thekr1s/esp8266_wordclock/images/handleiding/Aansluiting_1.jpg

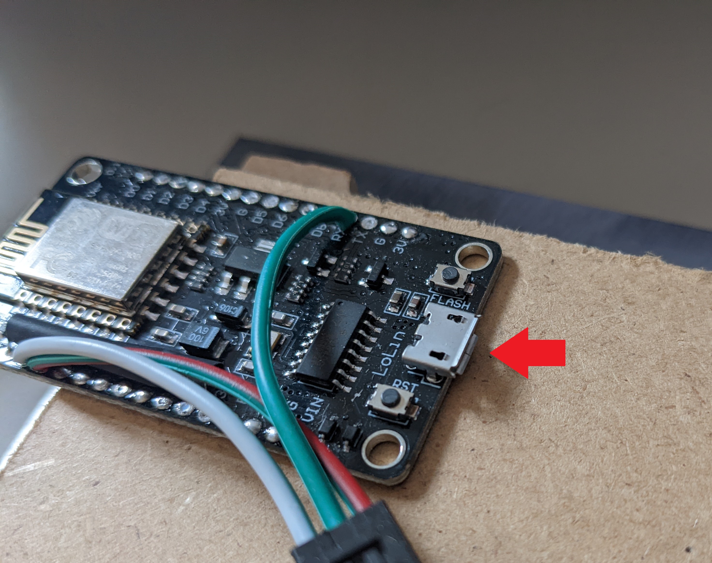
images/handleiding/Aansluiting_1.jpg
