thekr1s/esp8266_wordclock/images/rhu/2015-12-30 12.20.55.jpg

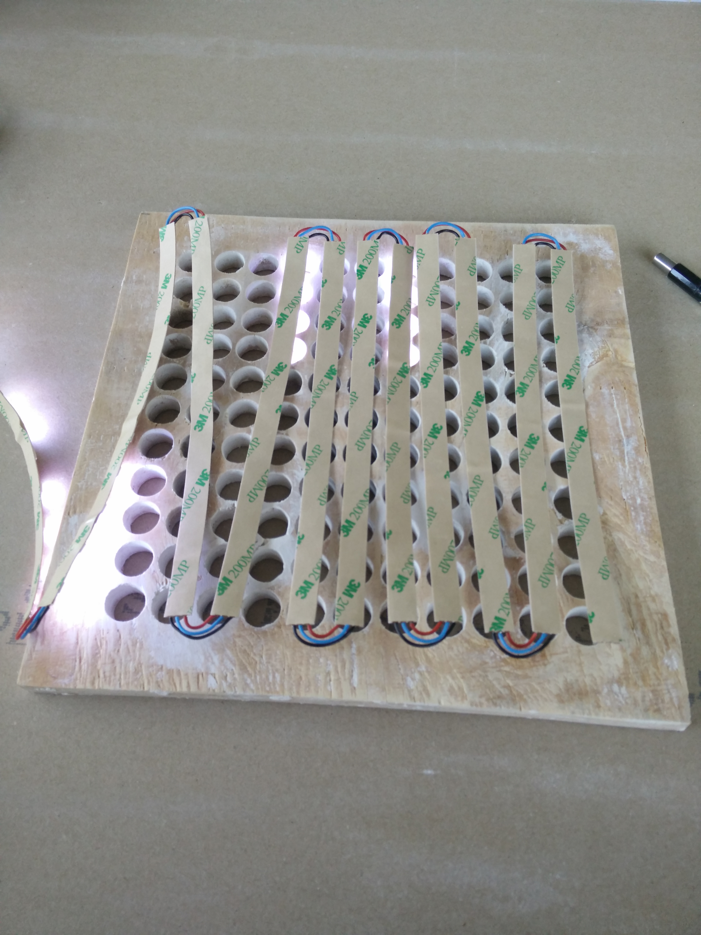
images/rhu/2015-12-30 12.20.55.jpg
