thekr1s/esp8266_wordclock/images/rhu/2016-01-02 10.30.15.jpg

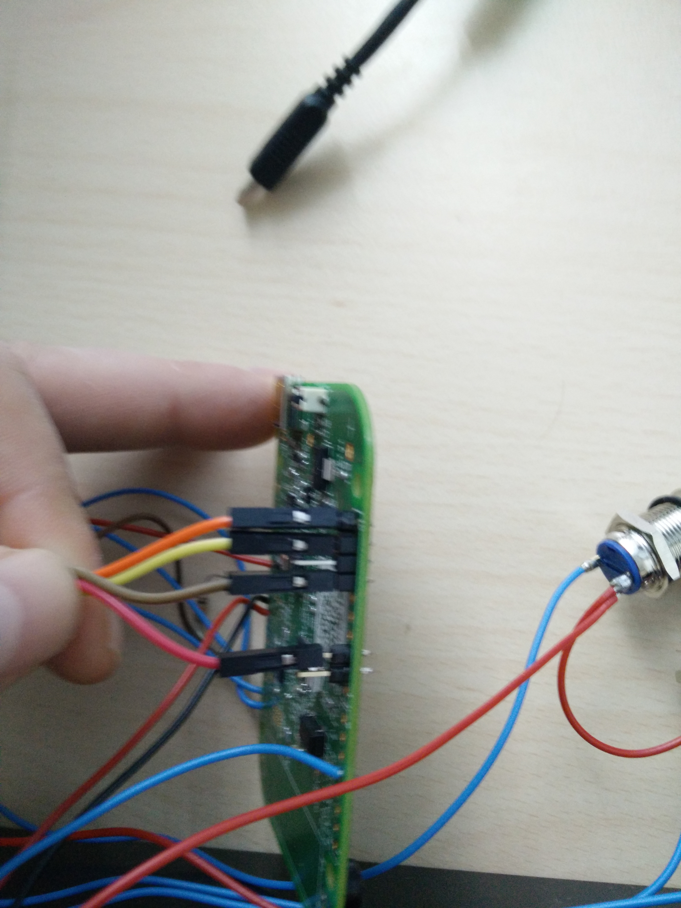
images/rhu/2016-01-02 10.30.15.jpg
