thekr1s/esp8266_wordclock/images/rwa/20151119_205304231.jpg

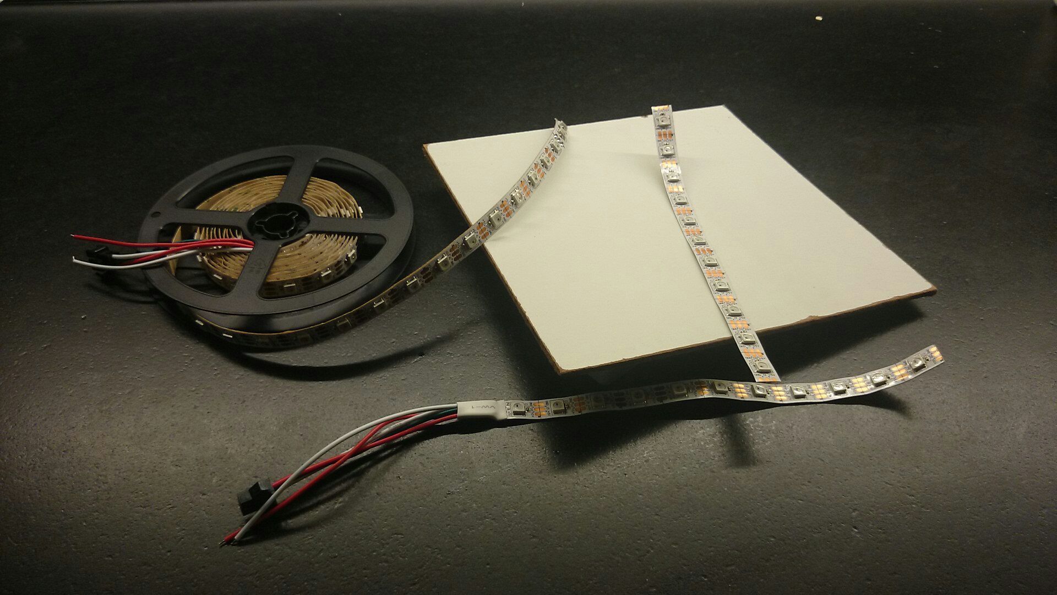
images/rwa/20151119_205304231.jpg
