thekr1s/esp8266_wordclock/images/rwa/20151119_211505547.jpg

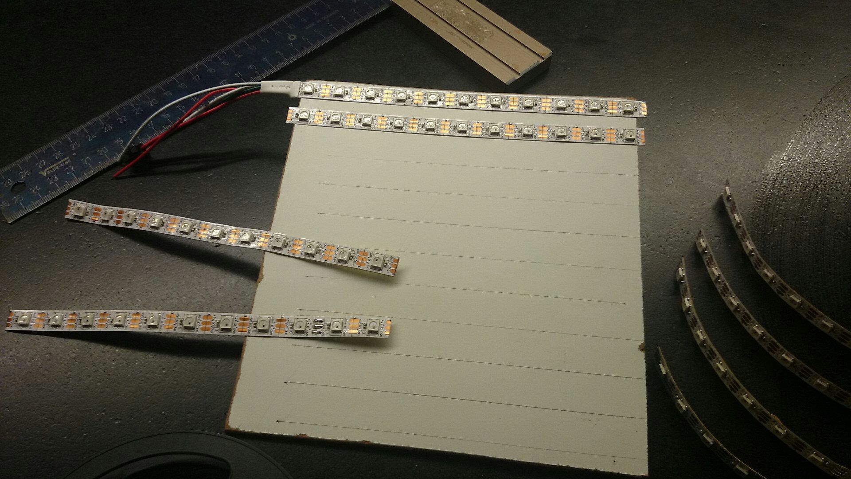
images/rwa/20151119_211505547.jpg
