thekr1s/esp8266_wordclock/images/rwa/20151119_221903994.jpg

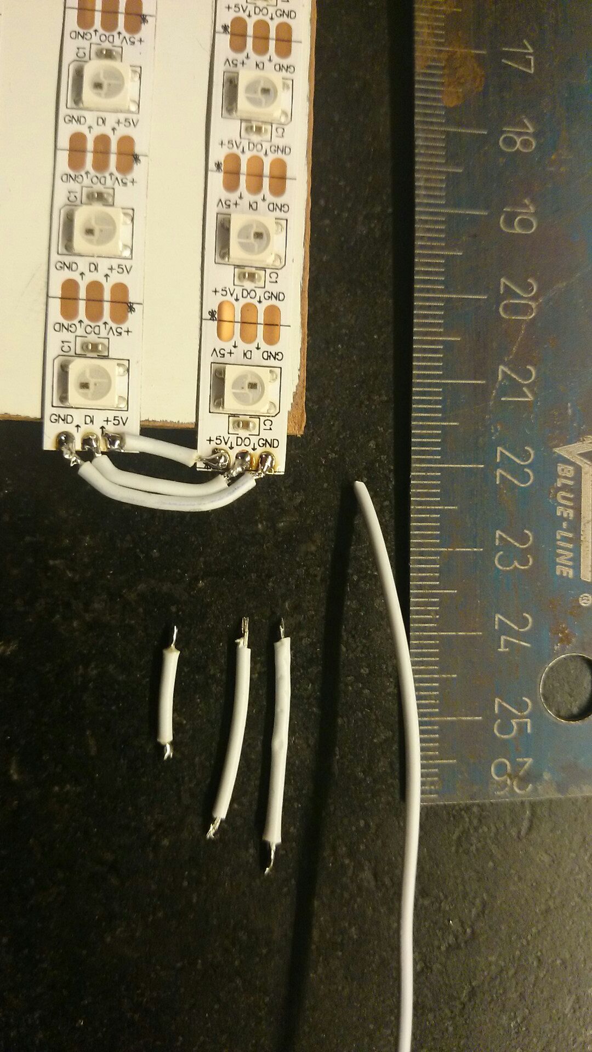
images/rwa/20151119_221903994.jpg
