thekr1s/esp8266_wordclock/images/rwa/20151119_222014442.jpg

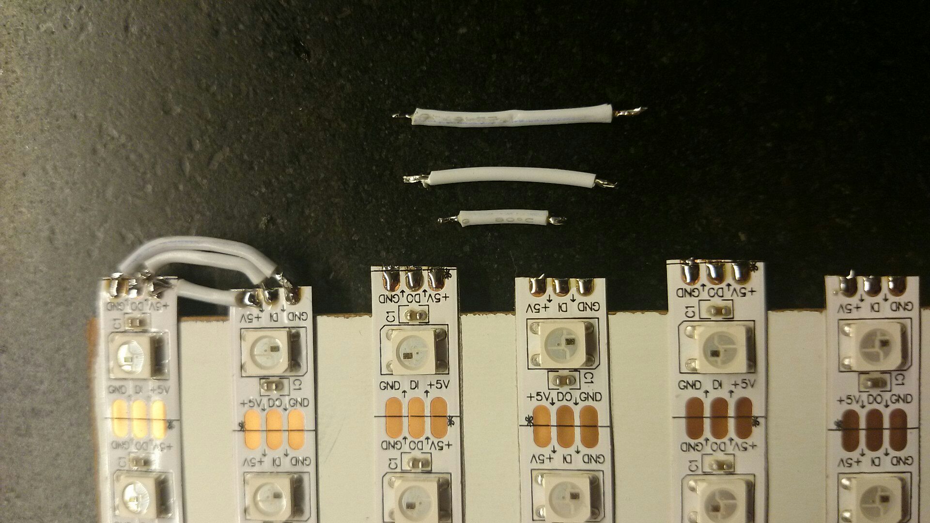
images/rwa/20151119_222014442.jpg
