thekr1s/esp8266_wordclock/images/rwa/20151120_000004302.jpg

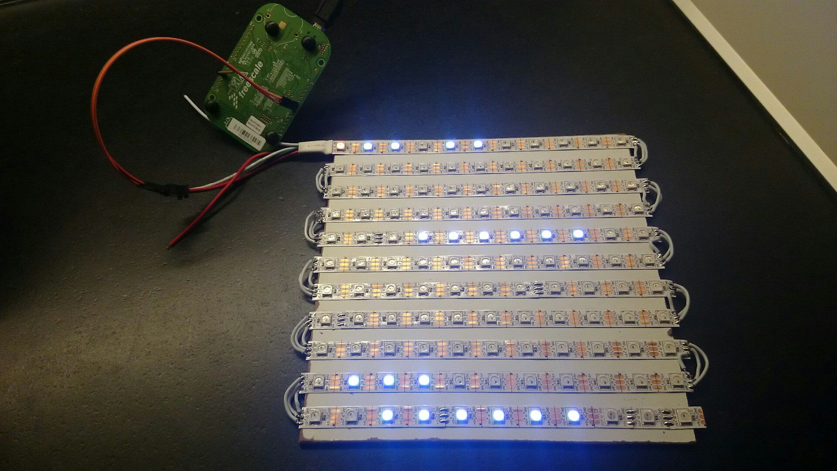
images/rwa/20151120_000004302.jpg
