thekr1s/esp8266_wordclock/images/rwa/20151120_195915981.jpg

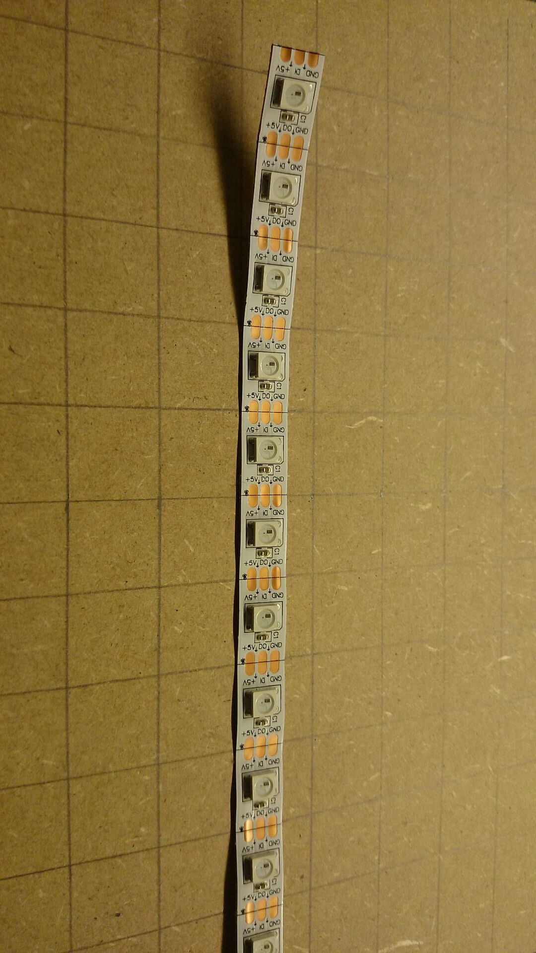
images/rwa/20151120_195915981.jpg
