thekr1s/esp8266_wordclock/images/rwa/20151120_200044932.jpg

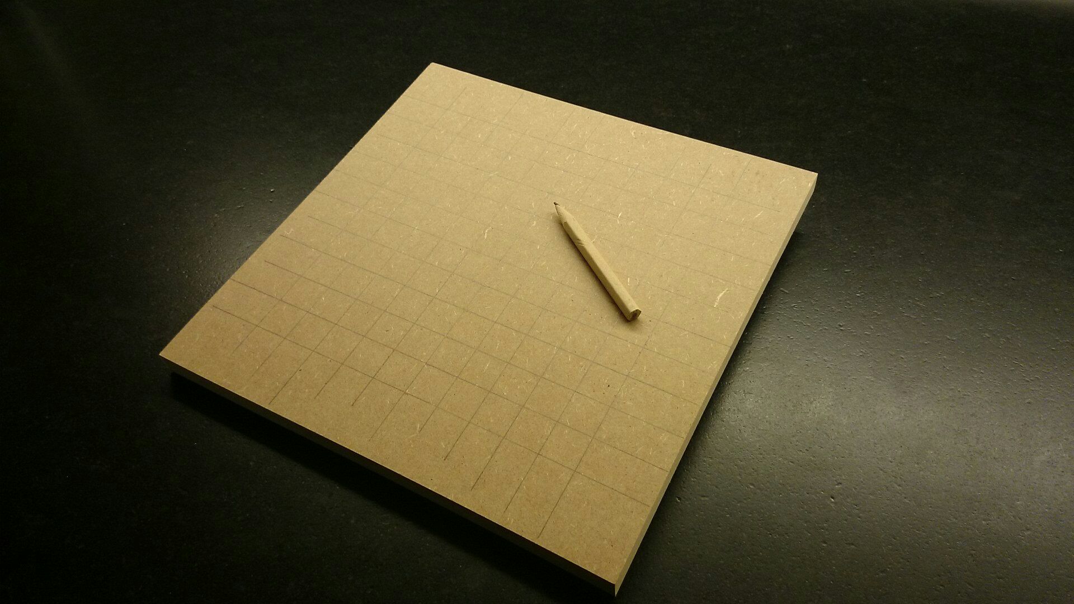
images/rwa/20151120_200044932.jpg
