thekr1s/esp8266_wordclock/images/rwa/20151120_201322455.jpg

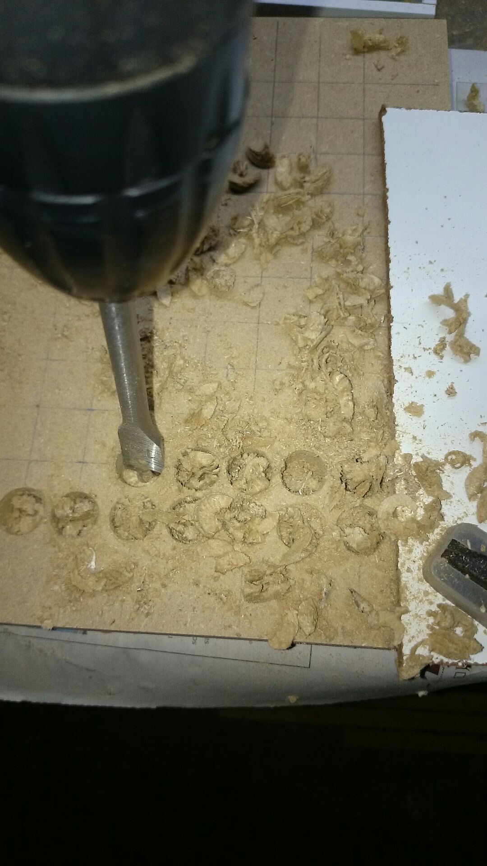
images/rwa/20151120_201322455.jpg
