thekr1s/esp8266_wordclock/images/rwa/20151120_202920301.jpg

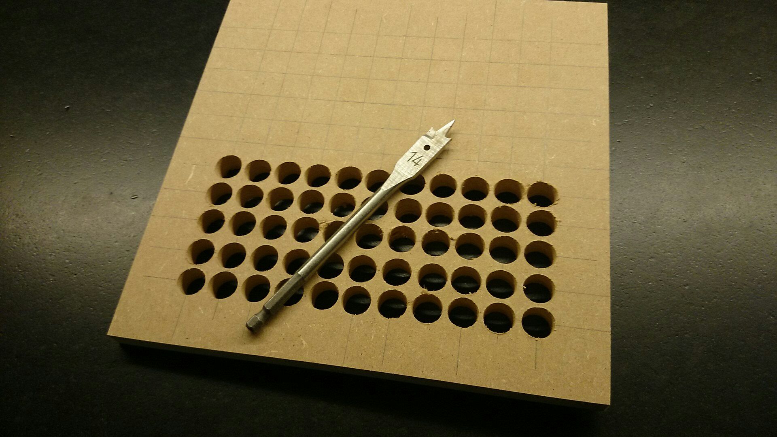
images/rwa/20151120_202920301.jpg
