thekr1s/esp8266_wordclock/images/rwa/20151214_203325597.jpg

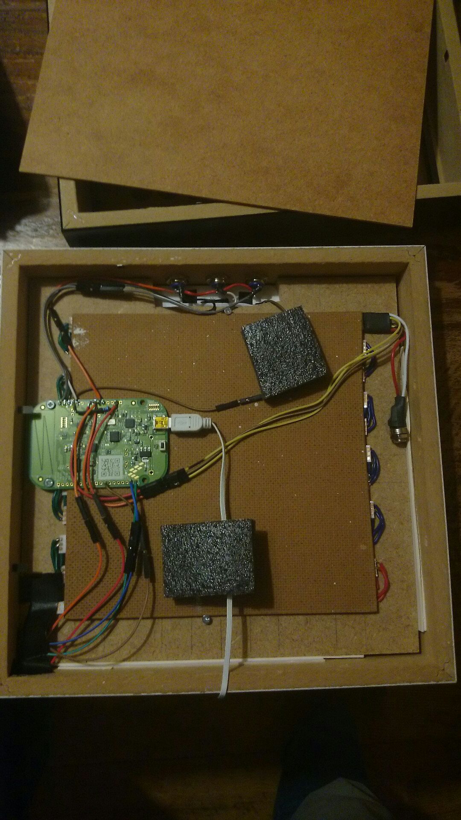
images/rwa/20151214_203325597.jpg
