thekr1s/esp8266_wordclock/images/rwa/20151217_220213394.jpg

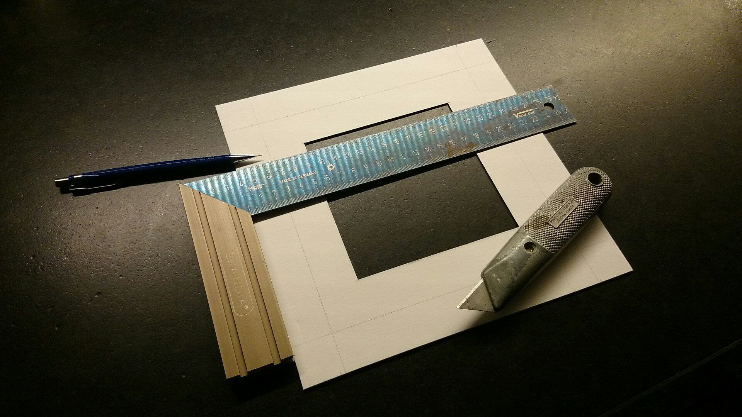
images/rwa/20151217_220213394.jpg
