thekr1s/esp8266_wordclock/images/rwa/20151217_220738030.jpg

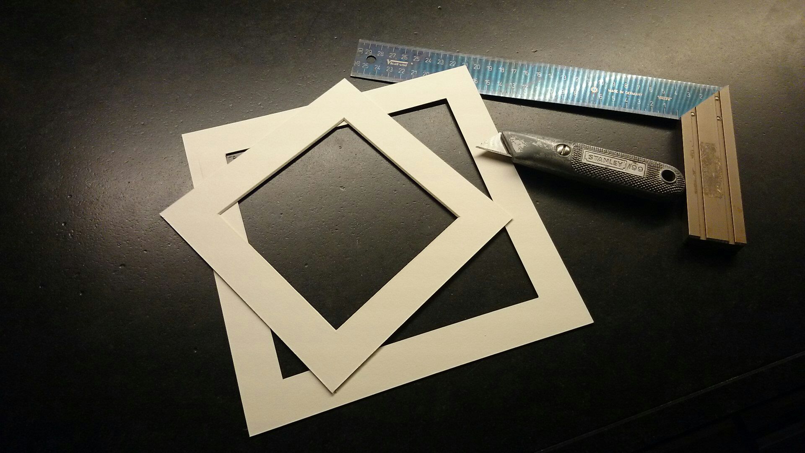
images/rwa/20151217_220738030.jpg
