thekr1s/esp8266_wordclock/hardware/led_divider/cambam_RWA/gatenboard_groot_13x13_half.dxf

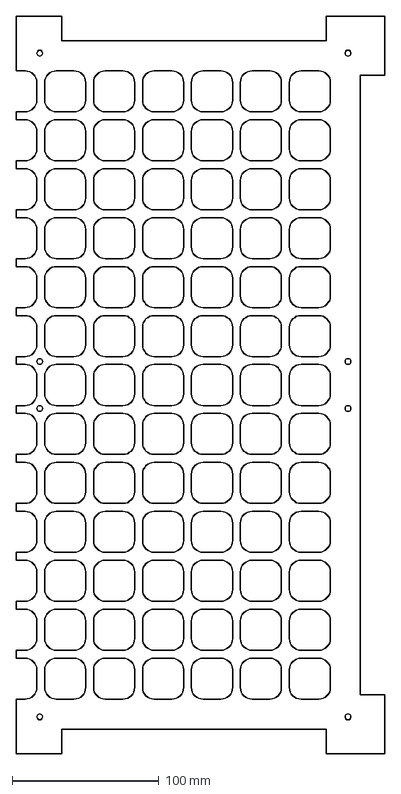
[picture p43: CAD file, 2019-11-26]
hardware/led_divider/cambam_RWA/gatenboard_groot_13x13_half.dxf
251.0 x 502.0 mm
