thekr1s/esp8266_wordclock/hardware/lettering_plates/FreeCAD_drawings/letterplate_11_11_freecad.dxf

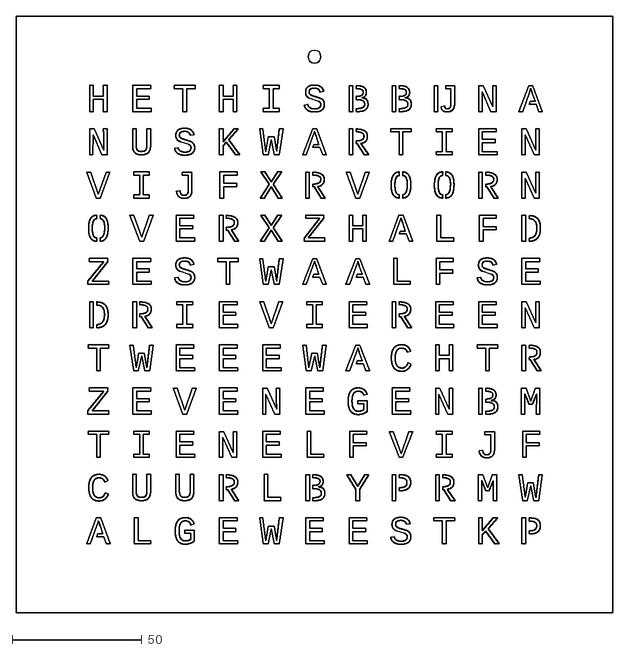
[picture p44: CAD file, 2020-07-10]
hardware/lettering_plates/FreeCAD_drawings/letterplate_11_11_freecad.dxf
230.0 x 230.0
