thekr1s/esp8266_wordclock/hardware/lettering_plates/QCAD_letterplaat/WOORDCLOCK_1.dxf

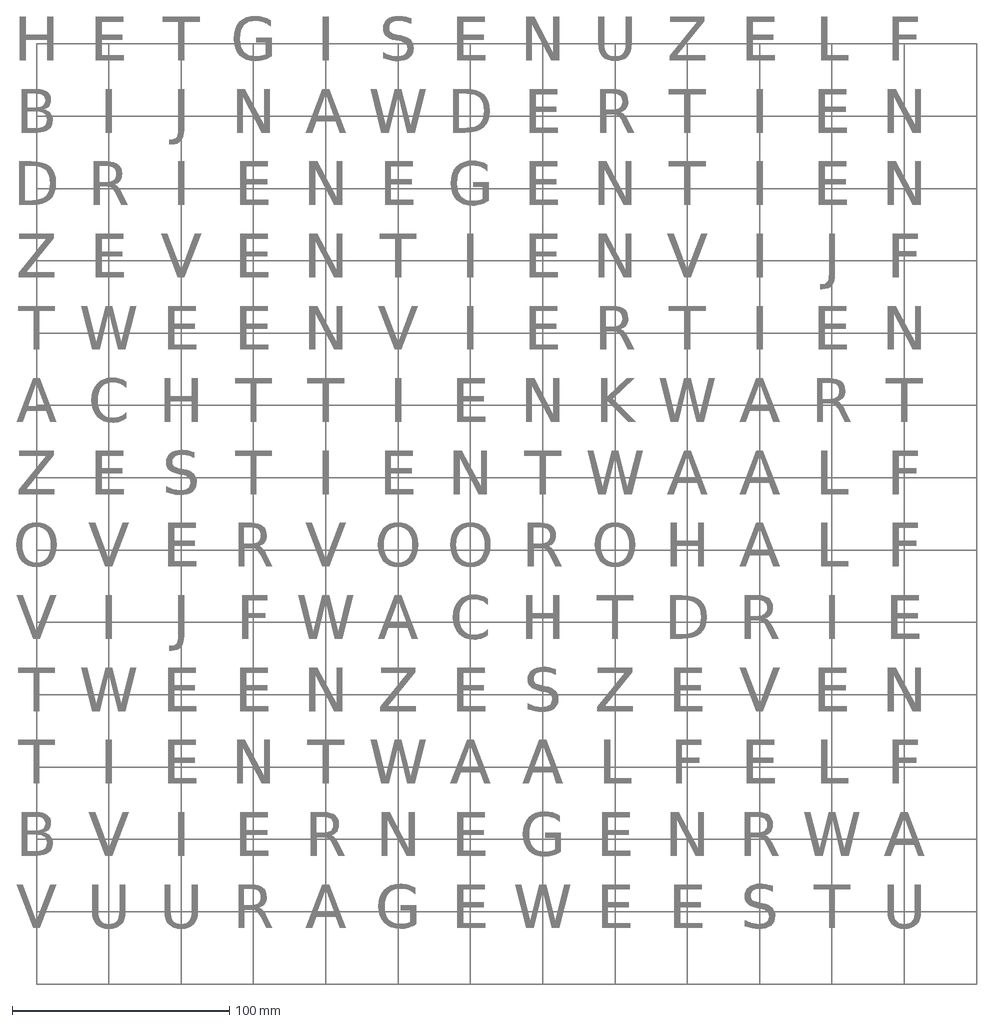
[picture p45: CAD file, 2019-11-20]
hardware/lettering_plates/QCAD_letterplaat/WOORDCLOCK_1.dxf
H
E
T
G
I
S
N
U
Z
L
F
W
D
A
R
B
J
V
K
C
O
