thekr1s/esp8266_wordclock/hardware/lettering_plates/FreeCAD_drawings/letterplate_13_13_fusion360_V4.dxf

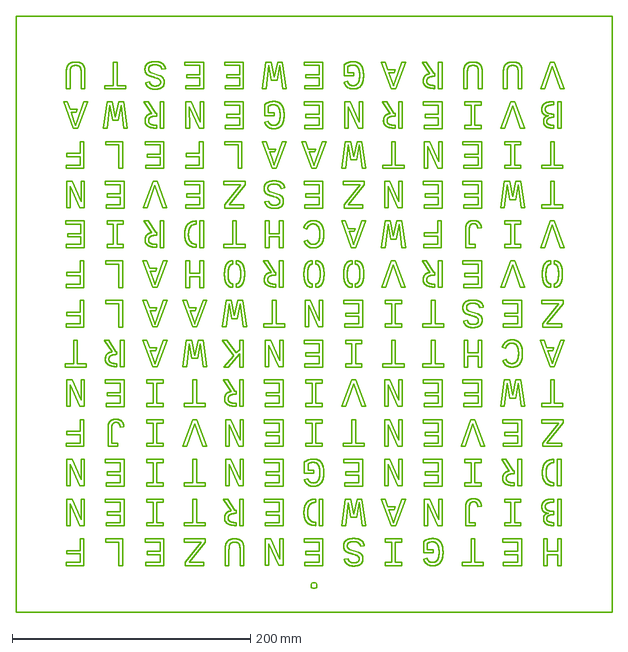
[picture p46: CAD file, 2020-04-23]
hardware/lettering_plates/FreeCAD_drawings/letterplate_13_13_fusion360_V4.dxf
500.0 x 500.0 mm
