thekr1s/esp8266_wordclock/hardware/lettering_plates/FreeCAD_drawings/letterplate_11_11_fusion360_v2.dxf

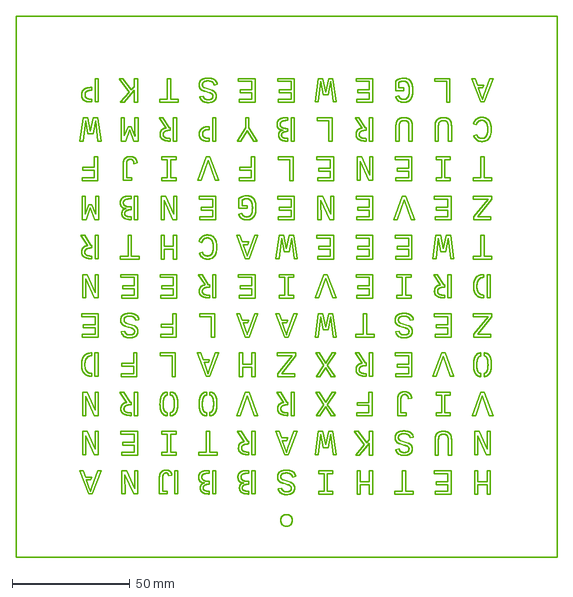
[picture p47: CAD file, 2020-04-23]
hardware/lettering_plates/FreeCAD_drawings/letterplate_11_11_fusion360_v2.dxf
230.0 x 230.0 mm
