thekr1s/esp8266_wordclock/hardware/lettering_plates/FreeCAD_drawings/letterplate_13_13.FCStd

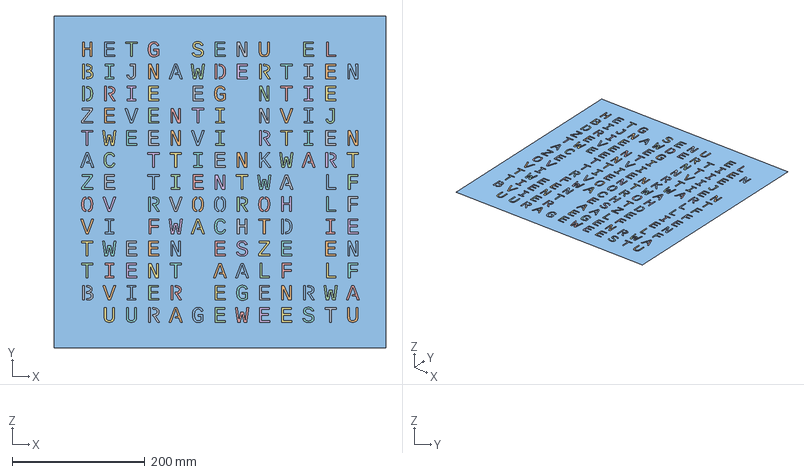
[picture p49: CAD file, 2020-04-08]
hardware/lettering_plates/FreeCAD_drawings/letterplate_13_13.FCStd
500.0 x 500.0 x 0 mm
Circle
ShapeString
ShapeString001
ShapeString002
ShapeString003
ShapeString004
ShapeString005
ShapeString006
ShapeString007
ShapeString008
ShapeString009
ShapeString010
ShapeString011
ShapeString012
ShapeString013
ShapeString014
ShapeString015
ShapeString016
ShapeString017
ShapeString018
ShapeString019
ShapeString020
ShapeString021
ShapeString022
ShapeString023
ShapeString024
ShapeString025
ShapeString026
ShapeString027
ShapeString028
ShapeString029
ShapeString030
ShapeString031
ShapeString032
ShapeString033
ShapeString034
ShapeString035
ShapeString036
ShapeString037
ShapeString038
ShapeString039
ShapeString040
ShapeString041
ShapeString042
ShapeString043
ShapeString044
ShapeString045
ShapeString046
ShapeString047
ShapeString048
ShapeString049
ShapeString050
ShapeString051
ShapeString052
ShapeString053
ShapeString054
ShapeString055
ShapeString056
ShapeString057
ShapeString058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
