thekr1s/esp8266_wordclock/wordclock/realtime_udp.c

#include <string.h>
#include <lwip/sockets.h>

#include "esp_glue.h"
#include "AddressableLedStrip.h"
#include "controller.h"
#include "tetris_pieces.h"

#define UDP_POORT 21324

uint16_t _nrOfRows;
uint16_t _nrOfCols;
uint16_t _ledStripLen;
//payload is 2 protocol bytes + 13x13 leds with R,G,B value
uint8_t payload[(WORDCLOCK_ROWS_MAX * WORDCLOCK_COLLS_MAX * 3) +2];

static void SetPixel(int index, uint8_t red, uint8_t green, uint8_t blue, uint8_t white) {
    // NOTE frames are stored as RGB show the white is missing, and dropped here
    // NOTE row 0 on the woordklok is the bottem so invert this
    int row = _nrOfRows - (index / _nrOfCols) - 1;
    int col = index % _nrOfRows;
    AlsSetLed(row, col, red, green, blue);
}

// https://github.com/Aircoookie/WLED/blob/main/wled00/udp.cpp
// UDP realtime: 1 warls 2 drgb 3 drgbw
static bool UDPFrameToPixelFrame(uint8_t* udpIn, size_t udpInLen) {
    

    if (udpInLen < 2) {
        printf("Invalid length\n");
        return false; // UDP package will not contain any pixel info
    }

    if (udpIn[0] < 0 || udpIn[0] > 5) {
        printf("Invalid protocol\n");
        return false; // Invalid protocol type
    }

    if (udpIn[1] == 0) {
        printf("Timeout is set to 0 so stop gam\n");
        ControllerGameSet(GAME_NONE);
        return false;
    }

    //warls - avoiding infinite "for" loop (unsigned underflow)    
    if ((udpIn[0] == 1) && (udpInLen > 5)) {
        for (size_t i = 2; i < udpInLen -3; i += 4) {
            SetPixel(udpIn[i], udpIn[i+1], udpIn[i+2], udpIn[i+3], 0);
        }
    } else if (udpIn[0] == 2 && (udpInLen > 4)) { //drgb
        uint16_t id = 0;
        for (size_t i = 2; i < udpInLen -2; i += 3) {
            SetPixel(id, udpIn[i], udpIn[i+1], udpIn[i+2], 0);
            id++; if (id >= _ledStripLen) break;
        }
    } else if ((udpIn[0] == 3) && (udpInLen > 5)) { //drgbw - avoiding infinite "for" loop (unsigned underflow)
        uint16_t id = 0;
        for (size_t i = 2; i < udpInLen -3; i += 4) {
            SetPixel(id, udpIn[i], udpIn[i+1], udpIn[i+2], udpIn[i+3]);
            id++; if (id >= _ledStripLen) break;
        }
    } else if (udpIn[0] == 4 && (udpInLen > 6)) { //dnrgb
        uint16_t id = ((udpIn[2] << 8) & 0xFF00) + (udpIn[3] & 0xFF);
        for (size_t i = 4; i < udpInLen -2; i += 3) {
            if (id >= _ledStripLen) break;
            SetPixel(id, udpIn[i], udpIn[i+1], udpIn[i+2], 0);
            id++;
        }
    } else if (udpIn[0] == 5 && (udpInLen > 7)) { //dnrgbw
        uint16_t id = ((udpIn[2] << 8) & 0xFF00) + (udpIn[3] & 0xFF);
        for (size_t i = 4; i < udpInLen -2; i += 4) {
            if (id >= _ledStripLen) break;
            SetPixel(id, udpIn[i], udpIn[i+1], udpIn[i+2], udpIn[i+3]);
            id++;
        }
    }
    return true;
}

void DoUdpRealtime() {
    struct sockaddr_in server_addr;
    struct timeval timeout = {60, 0};
    int udpSock = -1;
    int payloadLen;
    
    _nrOfRows = _displaySize[0];
    _nrOfCols = _displaySize[1];
    _ledStripLen = _displaySize[0] * _displaySize[1];  
    
    udpSock = socket(AF_INET, SOCK_DGRAM, IPPROTO_UDP);
    if (udpSock < 0) {
        printf("Error while creating Realtime UDP socket\n");
        return;
    }
    printf("Realtime UDP Socket created successfully\n");


    // Set the timeout for the socket
    if (setsockopt(udpSock, SOL_SOCKET, SO_RCVTIMEO, &timeout, sizeof(timeout)) < 0) {
        lwip_close(udpSock);
        return;
    }

    // Set port and IP:
    memset(&server_addr, 0, sizeof(server_addr));
    server_addr.sin_family = AF_INET;
    server_addr.sin_addr.s_addr = INADDR_ANY;
    server_addr.sin_port = htons(UDP_POORT);

    // Bind to the set port and IP:
    if(bind(udpSock, (struct sockaddr*)&server_addr, sizeof(server_addr)) < 0){
        printf("Couldn't bind to the port\n");
        lwip_close(udpSock);
        return;
    }

    printf("Realtime UDP socket listening on port: %d\n", UDP_POORT);

    AlsFill(0,0,0);
    AlsRefresh(ALSEFFECT_NONE);
    while (ControllerGameGet() == GAME_UDP_REALTIME) {
        payloadLen = recv(udpSock, payload, sizeof(payload), 0);
        if (payloadLen < 0 ){
            printf("Couldn't receive; error: %d\n", errno);
            Sleep(60);
            continue;
        }
        printf("Realtime UDP, recv frame len: %d\n", payloadLen);
        
        if (UDPFrameToPixelFrame(payload, payloadLen)) {
            ControllerSet(CONTROLLER_NONE); //eatch frame is a contoller action
            AlsRefresh(ALSEFFECT_NONE);
        }
    }
    printf("Realtime UDP game closed\n");
    lwip_close(udpSock);
}
