thekr1s/esp8266_wordclock/wordclock/displaySettings.h

/*
 * displaySettings.c
 *
 *  Created on: Oct 7, 2016
 *      Author: rutger.huijgen
 */
#ifndef DISPLAY_SETTINGS_H_
#define DISPLAY_SETTINGS_H_

#include "stdint.h"
#include "stdbool.h"

#define WORDCLOCK_ROWS_MAX 13 //The max values are used to allocate memory.
#define WORDCLOCK_COLLS_MAX 13
#define MAX_BRIGHTNESS_OFFSET 5
#define BRIGHTNESS_COUNT  12
#define MAX_URL_SIZE 100
#define MAX_PORT_SIZE 6
#define LEDSTRIP_GPIO_NR 5 //the hardware GPIO used for controlling the display

typedef struct {
    uint8_t r;
    uint8_t g;
    uint8_t b;
} TColor;

typedef enum {
    COLOR_WHITE,
    COLOR_BIT_PURPLE,
    COLOR_PURPLE,
    COLOR_MAGENTHA,
    COLOR_PINK,
    COLOR_RED,
    COLOR_ORANGE,
    COLOR_YELLOW,
    COLOR_YELLOW_GREEN,
    COLOR_GREEN,
    COLOR_BLUE_GREEN,
    COLOR_CYAN,
    COLOR_LIGHT_BLUE,
    COLOR_BLUE,
    COLOR_OFF
} TColorIdx;
#define COLOR_COUNT COLOR_OFF   //OFF is no color

uint8_t _displaySize[2]; //the cols and rows are set on init
uint8_t g_brightness;

TColor GetColorFromIdx(TColorIdx idx);
bool DisplayInNightMode(void);
bool SetBrightness(void);
uint8_t ApplyBrightness(uint8_t color);
uint8_t ApplyBgBrightness(uint8_t color);
void wordClockDisplay_init(void);

#endif //DISPLAY_SETTINGS_H_
