thekr1s/esp8266_wordclock/wordclock/hier_ben_ik.h

/*
 * hier_ben_ik.h
 *
 *  Created on: Oct 27, 2016
 *      Author: robert
 */

#ifndef HIER_BEN_IK_H_
#define HIER_BEN_IK_H_

void HbiGetDistAndAge(uint32_t* pDist, uint32_t* pAge);
void HbiGetLatLon(float* pLat, float* pLon);
void HbiInit();

#endif /* HIER_BEN_IK_H_ */
