thekr1s/esp8266_wordclock/wordclock/event_handler.h

/*
 * event_handler.h
 *
 *  Created on: Oct 24, 2016
 *      Author: robert
 */

#ifndef EVENT_HANDLER_H_
#define EVENT_HANDLER_H_

void EvtHdlInit();
void EvtHdlTimeChanged();
void EvtHdlButtonStateChange();

#endif /* EVENT_HANDLER_H_ */
