thekr1s/esp8266_wordclock/wordclock/ota_basic.h

/*
 * ota_basic.c
 *
 *  Created on: Oct 7, 2016
 *      Author: rutger.huijgen
 */

#ifndef OTA_BASIC_H_
#define OTA_BASIC_H_

void OtaUpdateInit(void);
bool OtaIsBusy(void);


#endif /* OTA_BASIC_H_ */
