thekr1s/esp8266_wordclock/wordclock/pacman.h

/*
 * pacman.h
 *
 *  Created on: Jun 21, 2015
 *      Author: robert.wassens
 */

#ifndef PACMAN_H_
#define PACMAN_H_

void PCPutPC(uint32_t row, uint32_t col, uint8_t r, uint8_t  g, uint8_t  b);

void PCPutGhost(uint32_t row, uint32_t col, uint8_t r, uint8_t  g, uint8_t  b);


#endif /* PACMAN_H_ */
